yuburoll/yuwol/images/yuwolHeader.jpg

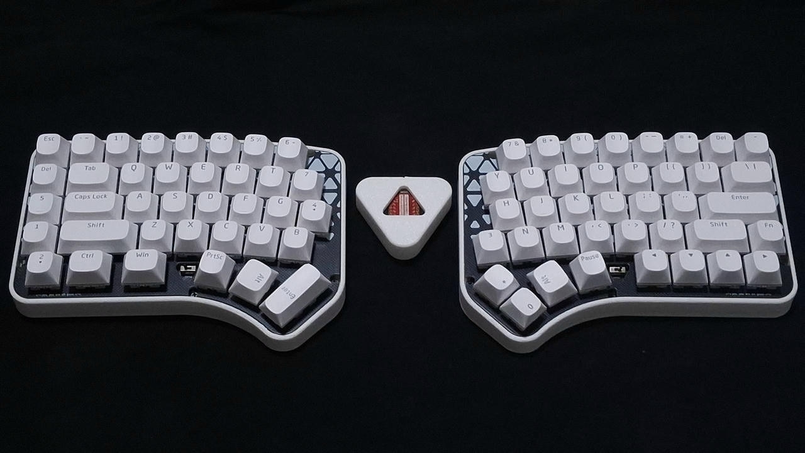
images/yuwolHeader.jpg
