yuburoll/yuwol/images/yuwolProfile1.jpg

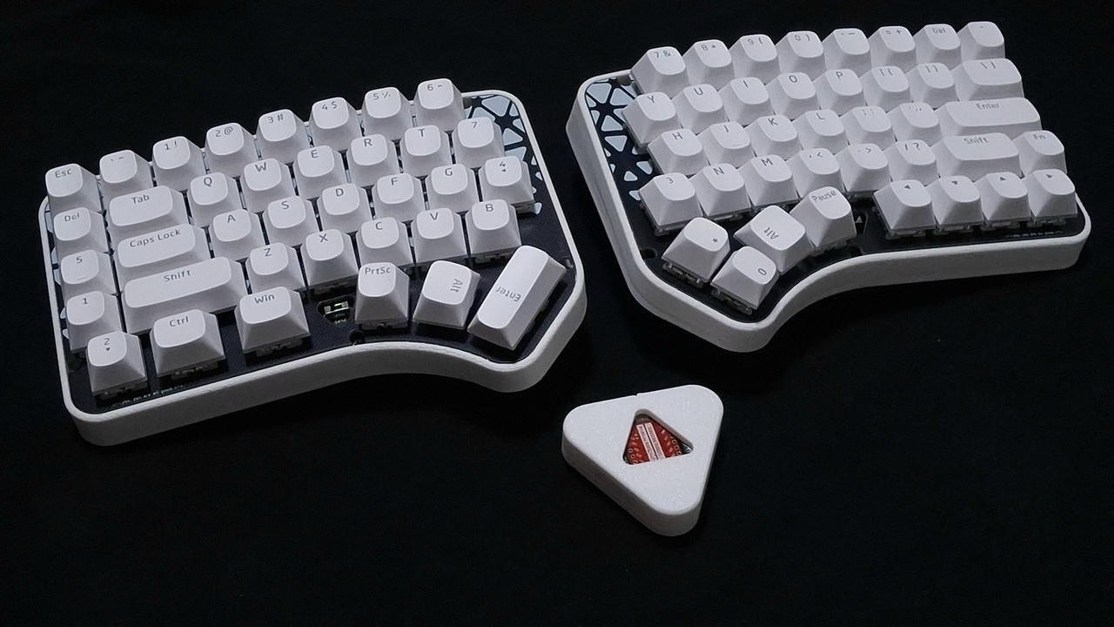
images/yuwolProfile1.jpg
