yuburoll/yuwol/images/yuwolProfile3.jpg

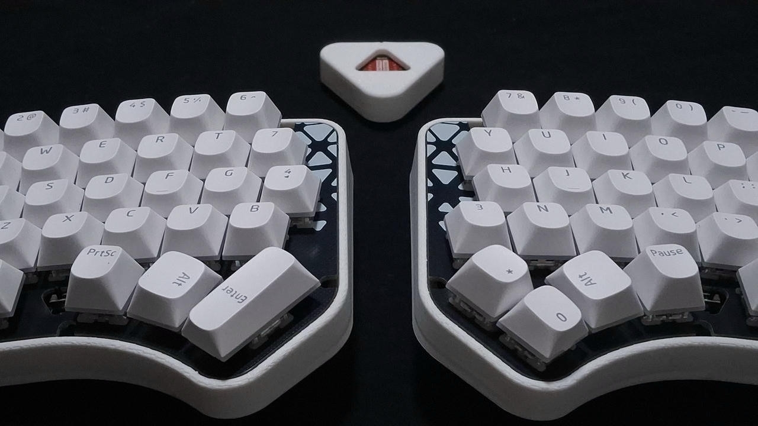
images/yuwolProfile3.jpg
