yuburoll/yuwol/case/3mf/yuwolPlates.3mf

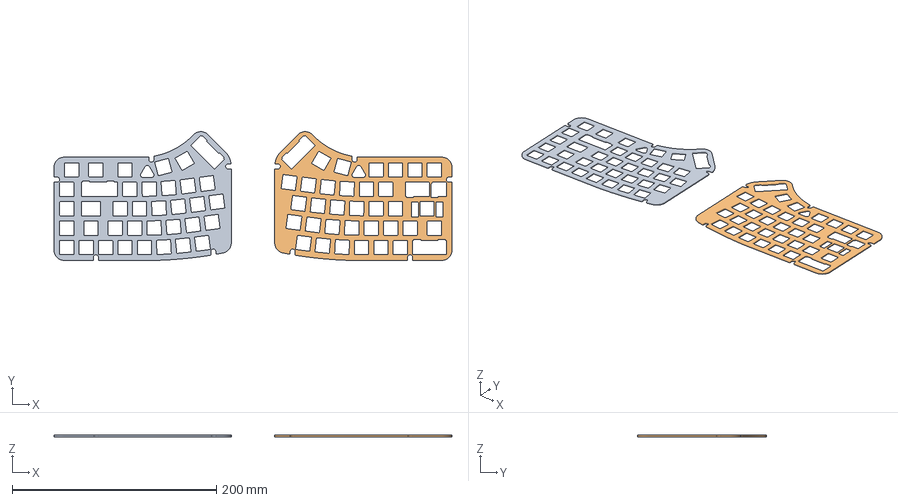
[picture p18: CAD file, 2026-10-02]
case/3mf/yuwolPlates.3mf
389.5 x 126.0 x 1.50 mm
yuwolPlateL.stl
yuwolPlateR.stl
