yuburoll/yuwol/case/dxf/yuwolPattern.dxf

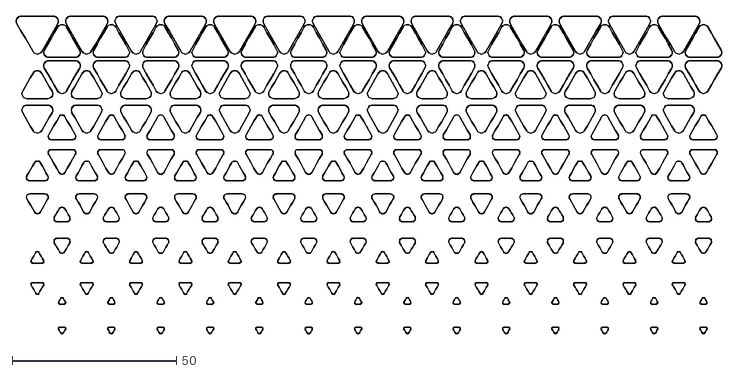
[picture p19: CAD file, 2026-09-17]
case/dxf/yuwolPattern.dxf
214.6 x 96.5
