yuburoll/yuwol/case/step/yuwolDongleTopInsert.stp

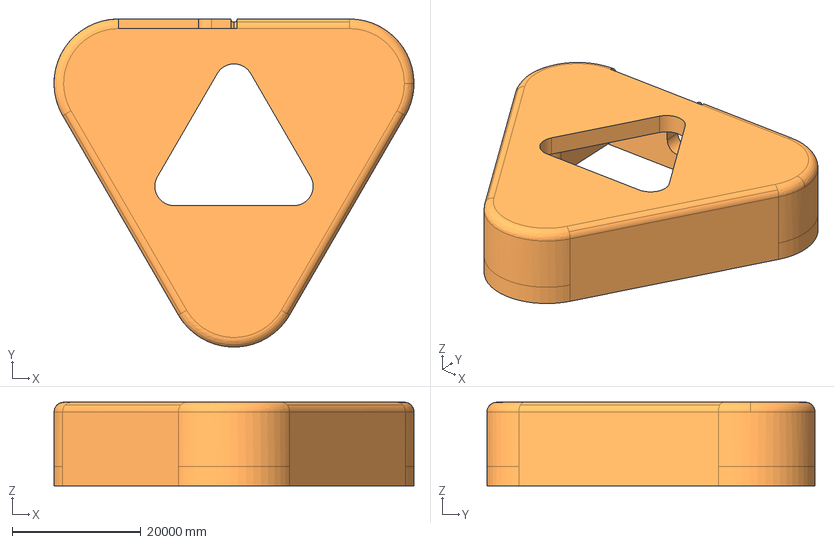
[picture p20: CAD file, 2026-09-30]
case/step/yuwolDongleTopInsert.stp
55942.4 x 50972.6 x 13000.0 mm
