yuburoll/yuwol/housing/step/yuwolCaseWirelessBatteryCoverL.stp

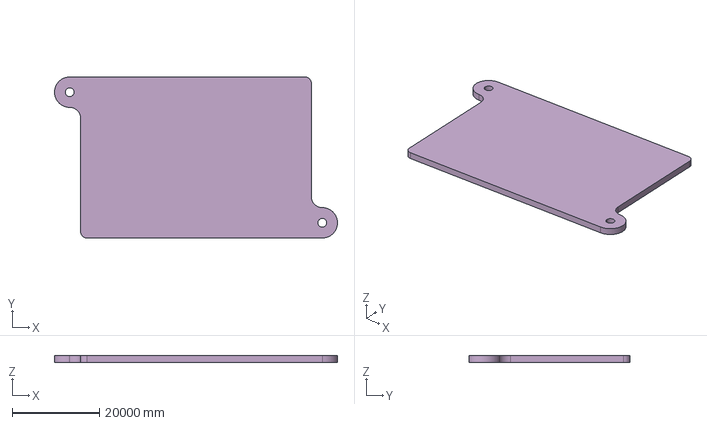
[picture p21: CAD file, 2026-09-30]
housing/step/yuwolCaseWirelessBatteryCoverL.stp
64994.8 x 37000.0 x 1500.0 mm
