yuburoll/yuwol/housing/stl/insert/yuwolDongleTopInsert.stl

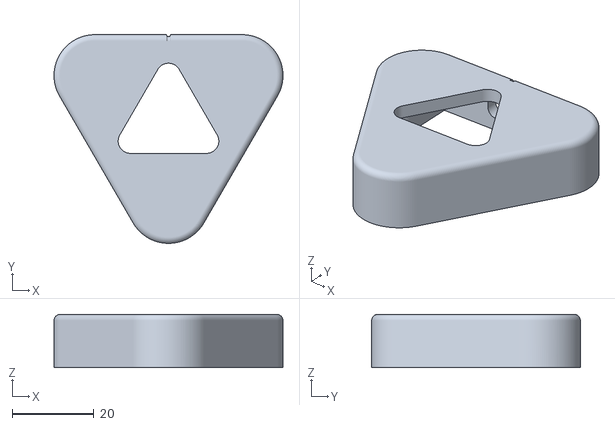
[picture p22: CAD file, 2026-09-30]
housing/stl/insert/yuwolDongleTopInsert.stl
55.9 x 51.0 x 13.0
