yuburoll/yuwol/case/3mf/yuwolWirelessInsert.3mf

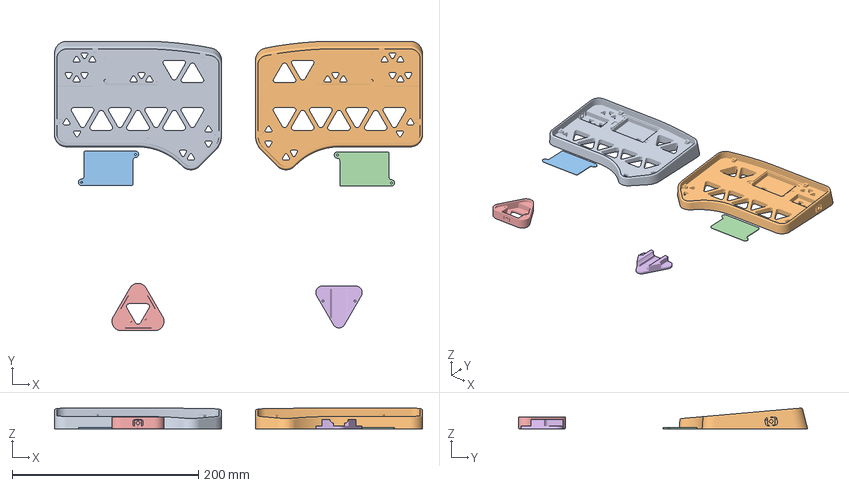
[picture p23: CAD file, 2026-10-02]
case/3mf/yuwolWirelessInsert.3mf
395.5 x 311.1 x 22.5 mm
yuwolCaseWirelessInsertBridgedL.stl
yuwolCaseWirelessInsertBridgedR.stl
yuwolCaseWirelessBatteryCoverL.stl
yuwolCaseWirelessBatteryCoverR.stl
yuwolDongleTopInsertBridged.stl
yuwolDongleBottomBridged.stl
