yuburoll/yuwol/case/dxf/yuwolTriangle.dxf

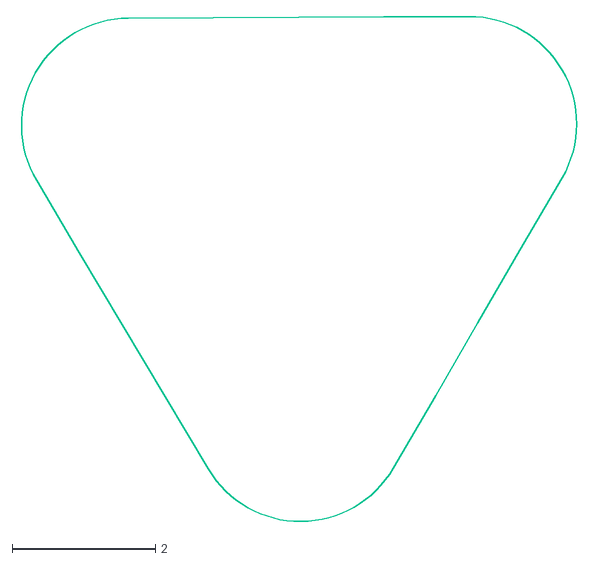
[picture p24: CAD file, 2026-09-17]
case/dxf/yuwolTriangle.dxf
7.89 x 7.06
