yuburoll/yuwol/case/stl/insert/yuwolDongleTopInsertBridged.stl

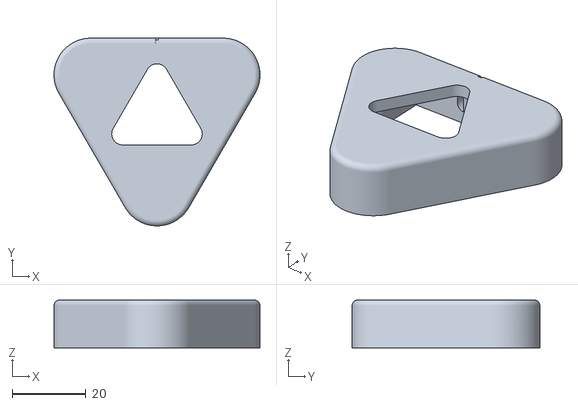
[picture p25: CAD file, 2026-09-30]
case/stl/insert/yuwolDongleTopInsertBridged.stl
55.9 x 51.0 x 13.0
