yuburoll/yuwol/Case/dxf/yuwolRightPlate.dxf

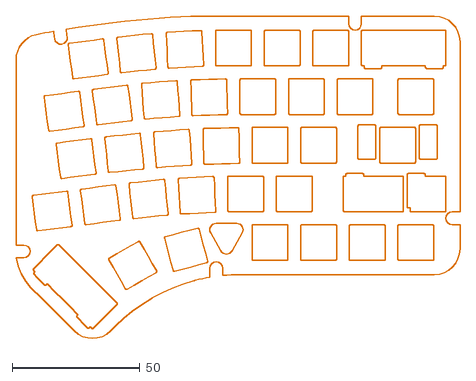
[picture p26: CAD file, 2026-09-17]
Case/dxf/yuwolRightPlate.dxf
173.5 x 127.0
