yuburoll/yuwol/case/step/yuwolPlateR.stp

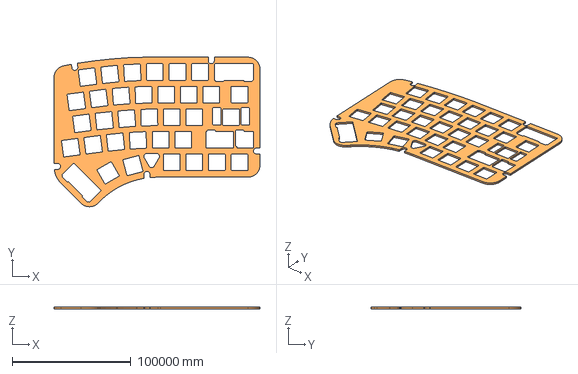
[picture p27: CAD file, 2026-09-30]
case/step/yuwolPlateR.stp
173500.0 x 125977.2 x 1500.0 mm
