yuburoll/yuwol/housing/step/yuwolCaseWiredInsertL.stp

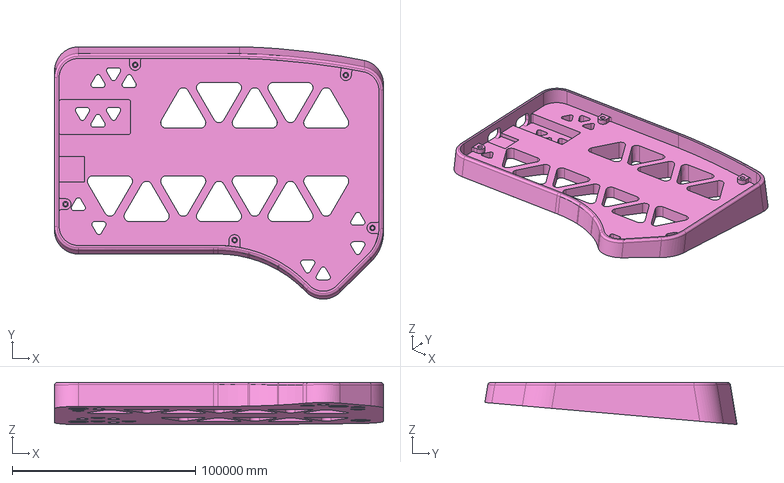
[picture p28: CAD file, 2026-09-30]
housing/step/yuwolCaseWiredInsertL.stp
179500.0 x 137628.1 x 23009.1 mm
