yuburoll/yuwol/Case/dxf/yuwolLeftPlate.dxf

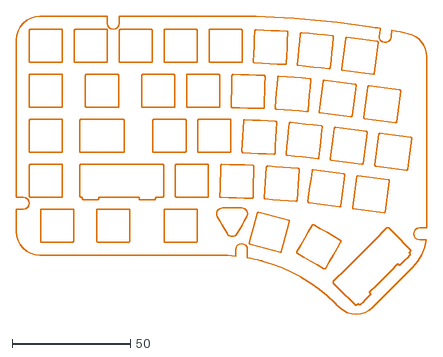
[picture p29: CAD file, 2026-09-17]
Case/dxf/yuwolLeftPlate.dxf
173.5 x 127.0
