yuburoll/yuwol/case/dxf/yuwolPositioning.dxf

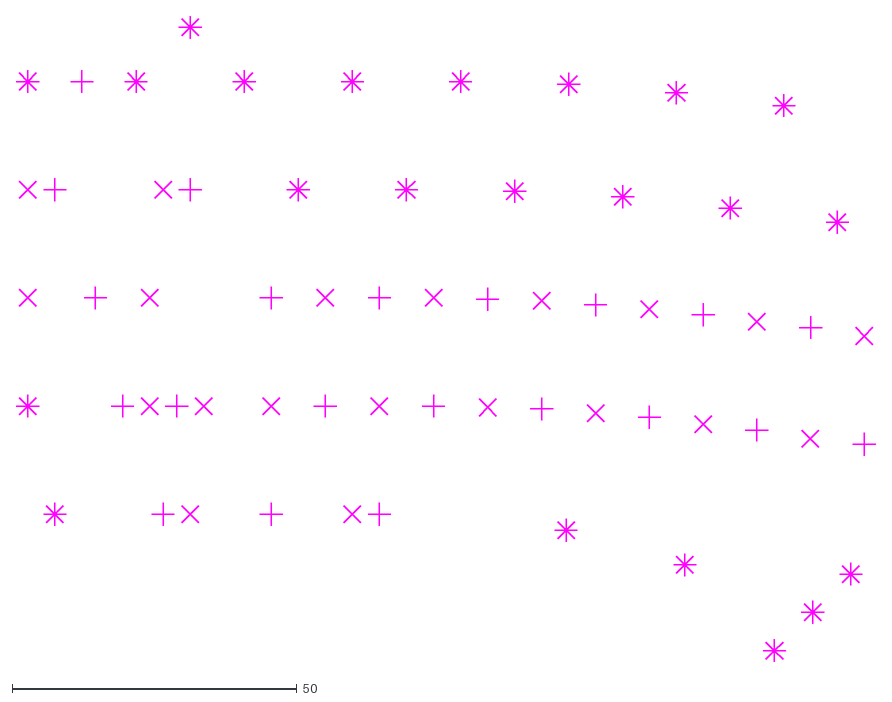
[picture p30: CAD file, 2026-09-07]
case/dxf/yuwolPositioning.dxf
150.9 x 113.4
