yuburoll/yuwol/images/yuwolBuildDevboard3.jpg

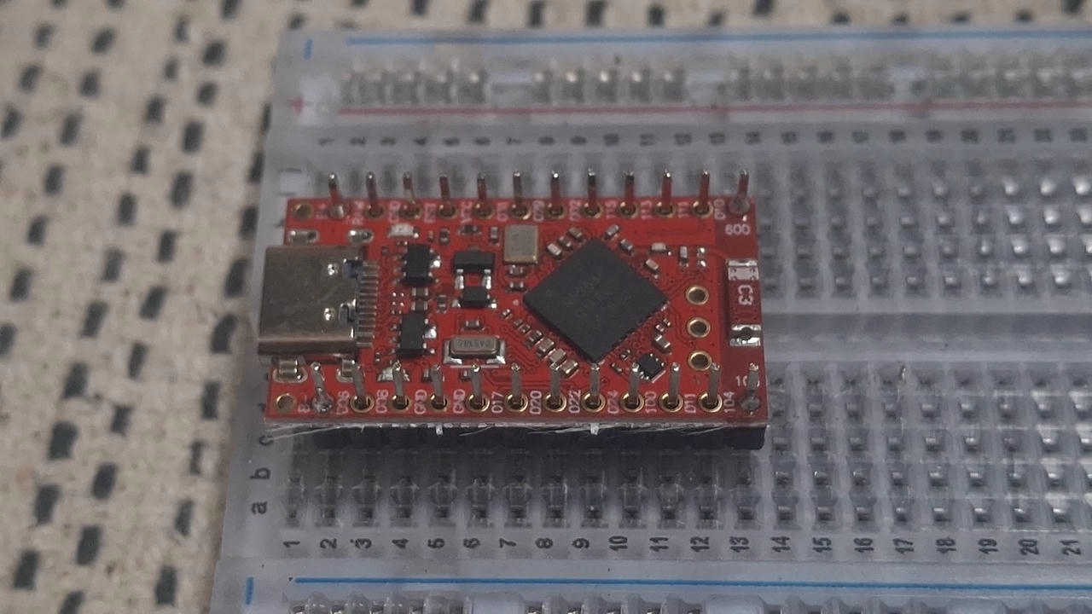
images/yuwolBuildDevboard3.jpg
