yuburoll/yuwol/images/yuwolBuildHeatinsert0.jpg

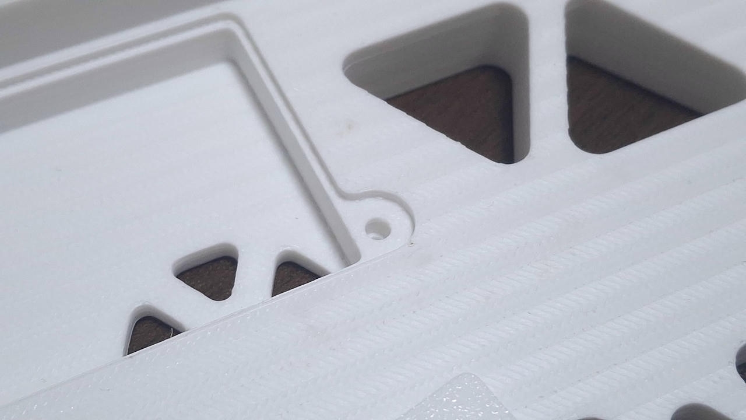
images/yuwolBuildHeatinsert0.jpg
