yuburoll/yuwol/images/yuwolBuildMolex0.jpg

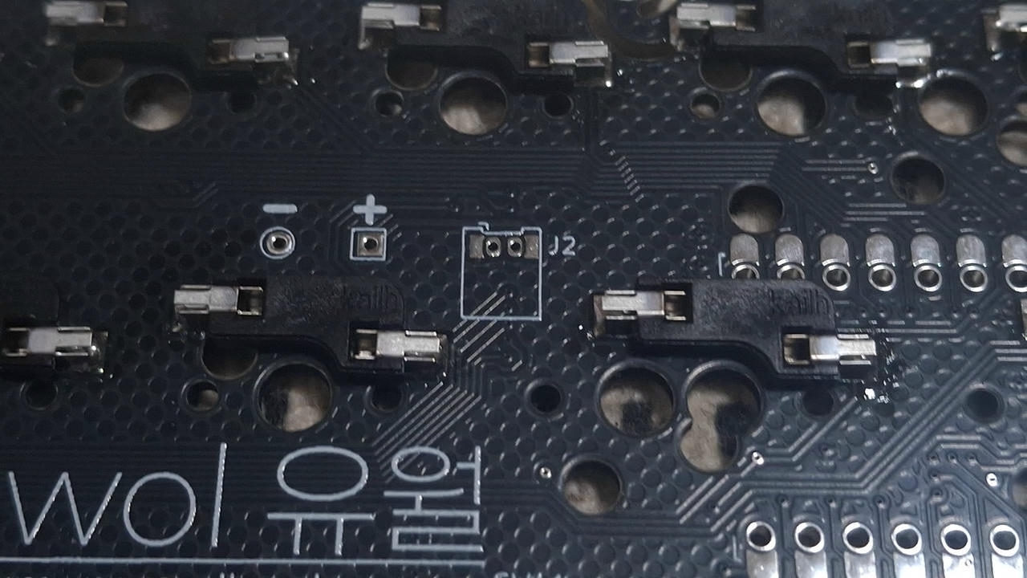
images/yuwolBuildMolex0.jpg
