yuburoll/yuwol/images/yuwolBuildPowSw0.jpg

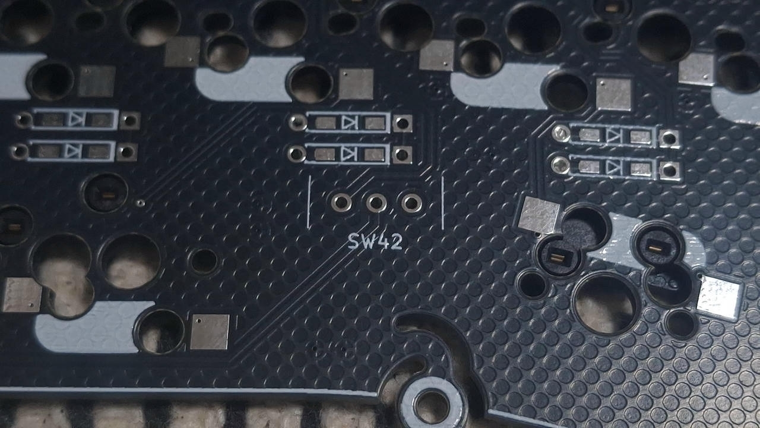
images/yuwolBuildPowSw0.jpg
