yuburoll/yuwol/images/yuwolBuildReset0.jpg

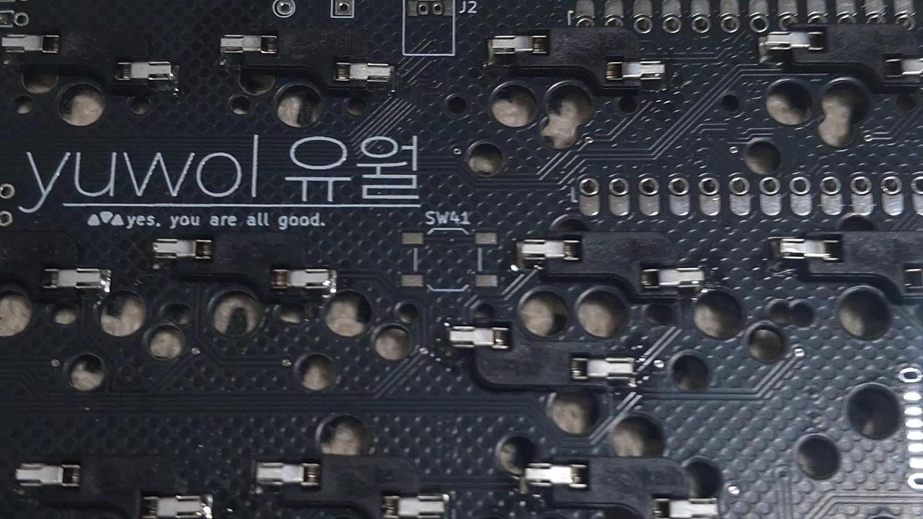
images/yuwolBuildReset0.jpg
