yuburoll/yuwol/images/yuwolBuildReset2.jpg

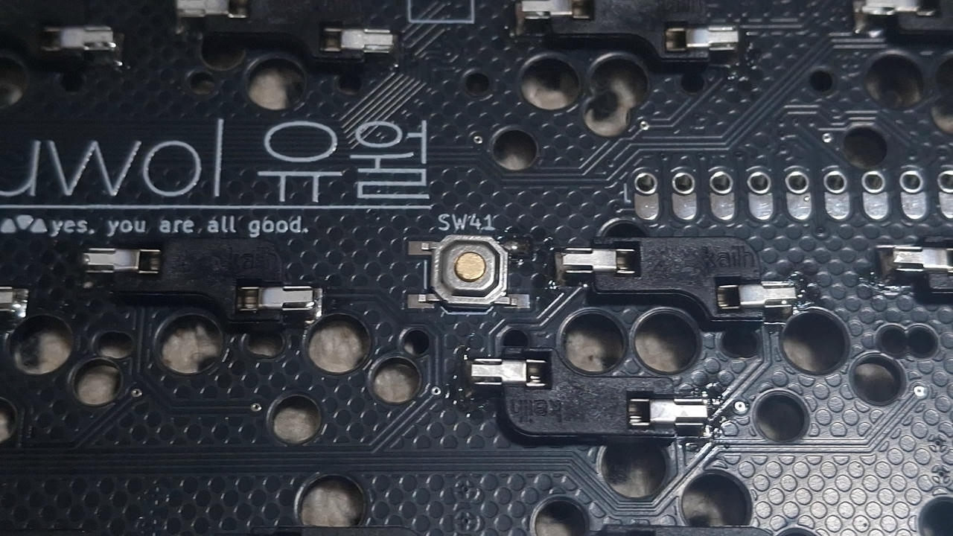
images/yuwolBuildReset2.jpg
